Friedsam2000/MatlabRaspy/Poster_Material/Robot_Assembled.png

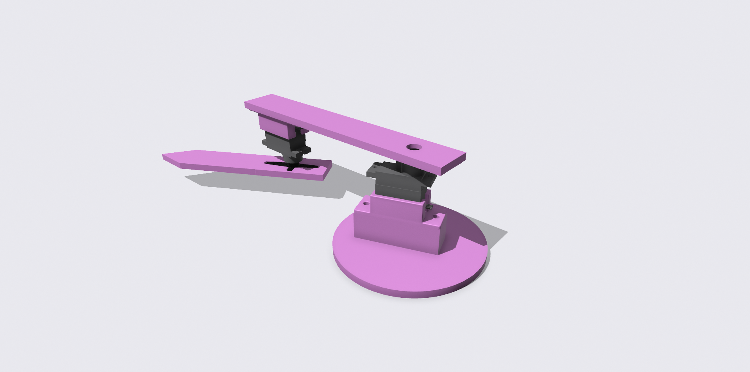
Poster_Material/Robot_Assembled.png
